DIY-Beatmungsgerat/diy-beatmungsgeraet/hardware/ventilator-model/Roller v2.step

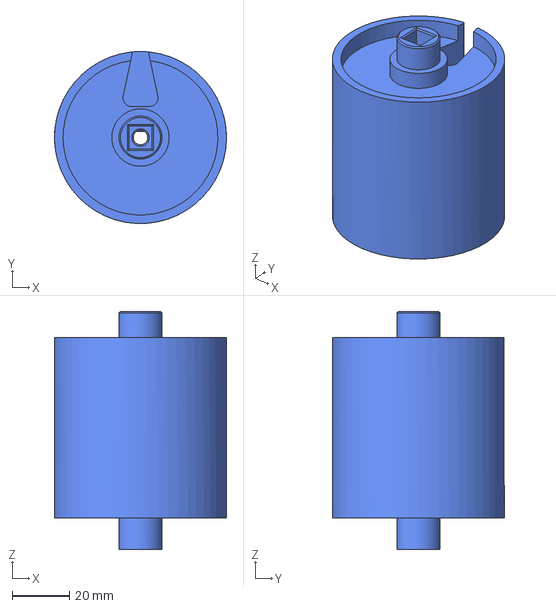
[picture p18: CAD file, 2020-03-22]
hardware/ventilator-model/Roller v2.step
60.0 x 60.0 x 83.0 mm
