DIY-Beatmungsgerat/diy-beatmungsgeraet/hardware/ventilator-model/DIN7049-ST4 v1.step

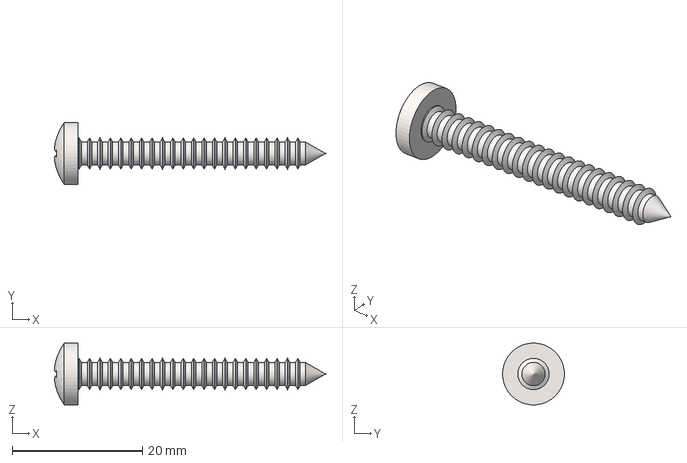
[picture p19: CAD file, 2020-03-22]
hardware/ventilator-model/DIN7049-ST4 v1.step
41.6 x 9.50 x 9.50 mm
